jhester/gobabygo/firmware/Src/datalog_application.c

/**
  ******************************************************************************
  * @file    datalog_application.c
  * @author  SRA - Central Labs
  * @version V2.0.0
  * @date    5-Feb-2019
  * @brief   This file provides a set of functions to handle the datalog
  *          application.
  ******************************************************************************
  * @attention
  *
  * <h2><center>&copy; COPYRIGHT(c) 2014 STMicroelectronics</center></h2>
  *
  * Licensed under MCD-ST Liberty SW License Agreement V2, (the "License");
  * You may not use this file except in compliance with the License.
  * You may obtain a copy of the License at:
  *
  *        http://www.st.com/software_license_agreement_liberty_v2
  *
  * Unless required by applicable law or agreed to in writing, software
  * distributed under the License is distributed on an "AS IS" BASIS,
  * WITHOUT WARRANTIES OR CONDITIONS OF ANY KIND, either express or implied.
  * See the License for the specific language governing permissions and
  * limitations under the License.
  *
  ******************************************************************************
  */

/* Includes ------------------------------------------------------------------*/
#include "datalog_application.h"
#include "main.h"
#include "usbd_cdc_interface.h"
#include "string.h"
#include "SensorTile.h"
#include <math.h>
    
/* FatFs includes component */
#include "ff_gen_drv.h"
#include "sd_diskio.h"

/* Includes ------------------------------------------------------------------*/

/* Private typedef -----------------------------------------------------------*/
typedef struct displayFloatToInt_s {
  int8_t sign; /* 0 means positive, 1 means negative*/
  uint32_t  out_int;
  uint32_t  out_dec;
} displayFloatToInt_t;

/* Private define ------------------------------------------------------------*/
#define MAX_BUF_SIZE 256  

/* Private variables ---------------------------------------------------------*/
static volatile uint8_t PushButtonDetected = 0;

static BSP_MOTION_SENSOR_Event_Status_t MotionStatus;

/* Private function prototypes -----------------------------------------------*/
static void MX_DataLogTerminal_Init(void);
    
FRESULT res;                                          /* FatFs function common result code */
uint32_t byteswritten, bytesread;                     /* File write/read counts */
FATFS SDFatFs;                                        /* File system object for SD card logical drive */
FIL MyFile;                                           /* File object */
FIL countFile;										  /* File that records the sequence of track files*/
char SDPath[4];                                       /* SD card logical drive path */
    
volatile uint8_t SD_Log_Enabled = 0;

char newLine[] = "\r\n";

extern volatile uint8_t no_H_HTS221;
extern volatile uint8_t no_T_HTS221;

/**
  * @brief  Start SD-Card demo
  * @param  None
  * @retval None
  */
void DATALOG_SD_Init(void)
{
  if(FATFS_LinkDriver(&SD_Driver, SDPath) == 0)
  {
    /* Register the file system object to the FatFs module */
    if(f_mount(&SDFatFs, (TCHAR const*)SDPath, 0) != FR_OK)
    {
      /* FatFs Initialization Error */
      while(1)
      {
        BSP_LED_On(LED1);
        HAL_Delay(500);
        BSP_LED_Off(LED1);
        HAL_Delay(100);
      }
    }
  }
}
  
/**
  * @brief  Start SD-Card demo
  * @param  None
  * @retval None
  */
char file_name[30] = {0};
uint8_t DATALOG_SD_Log_Enable(void)
{
  uint16_t sdcard_file_counter = 0;
  char header[] = "T [ms],AccX [mg],AccY [mg],AccZ [mg],GyroX [mdps],GyroY [mdps],GyroZ [mdps],MagX [mgauss],MagY [mgauss],MagZ [mgauss]\r\n";
  uint32_t byteswritten; /* written byte count */
  

  /* SD SPI CS Config */
  SD_IO_CS_Init();
  
  sdcard_file_counter=0;
  if(f_open(&countFile, "sequence_number.txt", FA_OPEN_EXISTING | FA_WRITE | FA_READ) == FR_OK){
	  if(f_read(&countFile, &sdcard_file_counter, sizeof(uint16_t), &byteswritten) == FR_OK){
		  sdcard_file_counter+=1;
	  }
	  f_close(&countFile);
  }
  if(f_open(&countFile, "sequence_number.txt", FA_CREATE_ALWAYS | FA_WRITE | FA_READ) != FR_OK)
	  return 0;
  f_write(&countFile, (const void*)&sdcard_file_counter, sizeof(uint16_t), &byteswritten);

  f_close(&countFile);


  sprintf(file_name, "%s%d%s", "SensorTile_Log_N", sdcard_file_counter, ".csv");

  HAL_Delay(500);

  if(f_open(&MyFile, (char const*)file_name, FA_CREATE_ALWAYS | FA_WRITE) != FR_OK)
  {
    return 0;
  }

  if(f_write(&MyFile, (const void*)&header, sizeof(header)-1, (void *)&byteswritten) != FR_OK)
  {
    return 0;
  }
  f_close(&MyFile);
  return 1;
}

//open/close the file when flag is 1
uint8_t DATALOG_SD_writeBuf(char *s, uint32_t size)
{
  uint32_t byteswritten;
  f_open(&MyFile, (char const*)file_name, FA_OPEN_APPEND | FA_WRITE);
  f_write(&MyFile, s, size, (void *)&byteswritten);
  f_close(&MyFile);
  return 0;
}


/**
  * @brief  Disable SDCard Log
  * @param  None
  * @retval None
  */
void DATALOG_SD_Log_Disable(void)
{
  f_close(&MyFile);
  
  /* SD SPI Config */
  SD_IO_CS_DeInit();
}

void DATALOG_SD_DeInit(void)
{
  FATFS_UnLinkDriver(SDPath);
}

/**
  * @brief  Write New Line to file
  * @param  None
  * @retval None
  */
void DATALOG_SD_NewLine(void)
{
  uint32_t byteswritten; /* written byte count */
  f_write(&MyFile, (const void*)&newLine, 2, (void *)&byteswritten);
}

 
int32_t getSensorsData( T_SensorsData *mptr)
{
  int32_t ret = BSP_ERROR_NONE;
  mptr->ms_counter = HAL_GetTick();
  
  /* Get Data from Sensors */  
  if ( BSP_MOTION_SENSOR_GetAxes(LSM6DSM_0, MOTION_ACCELERO, &mptr->acc ) == BSP_ERROR_COMPONENT_FAILURE )
  {
    mptr->acc.x = 0;
    mptr->acc.y = 0;
    mptr->acc.z = 0;
    ret = BSP_ERROR_COMPONENT_FAILURE;
  }
  
  if ( BSP_MOTION_SENSOR_GetAxes(LSM6DSM_0, MOTION_GYRO, &mptr->gyro ) == BSP_ERROR_COMPONENT_FAILURE )
  {
    mptr->gyro.x = 0;
    mptr->gyro.y = 0;
    mptr->gyro.z = 0;
    ret = BSP_ERROR_COMPONENT_FAILURE;
  }
  
  if ( BSP_MOTION_SENSOR_GetAxes(LSM303AGR_MAG_0, MOTION_MAGNETO, &mptr->mag ) == BSP_ERROR_COMPONENT_FAILURE )
  {
    mptr->mag.x = 0;
    mptr->mag.y = 0;
    mptr->mag.z = 0;
    ret = BSP_ERROR_COMPONENT_FAILURE;
  }
  
//  if ( BSP_ENV_SENSOR_GetValue(LPS22HB_0, ENV_PRESSURE, &mptr->pressure ) == BSP_ERROR_COMPONENT_FAILURE )
//  {
//    mptr->pressure = 0.0f;
//    ret = BSP_ERROR_COMPONENT_FAILURE;
//  }
//
//  if(!no_T_HTS221)
//  {
//    if ( BSP_ENV_SENSOR_GetValue(HTS221_0, ENV_TEMPERATURE, &mptr->temperature ) == BSP_ERROR_COMPONENT_FAILURE )
//    {
//      mptr->temperature = 0.0f;
//      ret = BSP_ERROR_COMPONENT_FAILURE;
//    }
//  }
//  else
//  {
//    if ( BSP_ENV_SENSOR_GetValue(LPS22HB_0, ENV_TEMPERATURE, &mptr->temperature ) == BSP_ERROR_COMPONENT_FAILURE )
//    {
//      mptr->temperature = 0.0f;
//      ret = BSP_ERROR_COMPONENT_FAILURE;
//    }
//  }
//
//  if(!no_H_HTS221)
//  {
//    if ( BSP_ENV_SENSOR_GetValue(HTS221_0, ENV_HUMIDITY, &mptr->humidity ) == BSP_ERROR_COMPONENT_FAILURE )
//    {
//      mptr->humidity = 0.0f;
//      ret = BSP_ERROR_COMPONENT_FAILURE;
//    }
//  }
  return ret;
}

/**
* @brief  Splits a float into two integer values.
* @param  in the float value as input
* @param  out_int the pointer to the integer part as output
* @param  out_dec the pointer to the decimal part as output
* @param  dec_prec the decimal precision to be used
* @retval None
*/
void floatToInt( float in, int32_t *out_int, int32_t *out_dec, int32_t dec_prec )
{
  *out_int = (int32_t)in;
  if(in >= 0.0f)
  {
    in = in - (float)(*out_int);
  }
  else
  {
    in = (float)(*out_int) - in;
  }
  *out_dec = (int32_t)trunc(in * pow(10, dec_prec));
}

int32_t DoubleTap(void)
{
  int32_t ret = 0;
  BSP_MOTION_SENSOR_Get_Event_Status(LSM6DSM_0, &MotionStatus);
  if (MotionStatus.DoubleTapStatus==1)
  {
    ret = 1;
  }
  
  return ret;
}

void MX_X_CUBE_MEMS1_Init(void)
{
  MX_DataLogTerminal_Init();
}


/**
  * @brief  Initialize the DataLogTerminal application
  * @retval None
  */
void MX_DataLogTerminal_Init(void)
{
  BSP_MOTION_SENSOR_Init(LSM303AGR_MAG_0, MOTION_MAGNETO);
  BSP_MOTION_SENSOR_SetOutputDataRate(LSM303AGR_MAG_0, MOTION_MAGNETO, LSM303AGR_MAG_ODR);
  BSP_MOTION_SENSOR_SetFullScale(LSM303AGR_MAG_0, MOTION_MAGNETO, LSM303AGR_MAG_FS);
  
  BSP_MOTION_SENSOR_Init(LSM6DSM_0, MOTION_ACCELERO | MOTION_GYRO);
  BSP_MOTION_SENSOR_SetOutputDataRate(LSM6DSM_0, MOTION_ACCELERO, LSM6DSM_ACC_ODR);
  BSP_MOTION_SENSOR_SetFullScale(LSM6DSM_0, MOTION_ACCELERO, LSM6DSM_ACC_FS);
  BSP_MOTION_SENSOR_SetOutputDataRate(LSM6DSM_0, MOTION_GYRO, LSM6DSM_GYRO_ODR);
  BSP_MOTION_SENSOR_SetFullScale(LSM6DSM_0, MOTION_GYRO, LSM6DSM_GYRO_FS);

//  if (BSP_ENV_SENSOR_Init(HTS221_0, ENV_TEMPERATURE | ENV_HUMIDITY) == BSP_ERROR_NONE)
//  {
//    BSP_ENV_SENSOR_SetOutputDataRate(HTS221_0, ENV_TEMPERATURE, HTS221_ODR);
//    BSP_ENV_SENSOR_SetOutputDataRate(HTS221_0, ENV_HUMIDITY, HTS221_ODR);
//  }
//  else
//  {
//    no_H_HTS221 = 1;
//    no_T_HTS221 = 1;
//  }
  
//  BSP_ENV_SENSOR_Init(LPS22HB_0, ENV_TEMPERATURE | ENV_PRESSURE);
//  BSP_ENV_SENSOR_SetOutputDataRate(LPS22HB_0, ENV_TEMPERATURE, LPS22HB_ODR);
//  BSP_ENV_SENSOR_SetOutputDataRate(LPS22HB_0, ENV_PRESSURE, LPS22HB_ODR);
            
//  BSP_MOTION_SENSOR_Enable_Double_Tap_Detection(LSM6DSM_0, BSP_MOTION_SENSOR_INT2_PIN);
}

/**
  * @}
  */

/**
  * @}
  */

/**
  * @}
  */

/**
  * @}
  */

/************************ (C) COPYRIGHT STMicroelectronics *****END OF FILE****/
